JustAGlitchFL/Mix/mix/mix.kicad_sch

## KiCad design mix/mix.kicad_sch (2025-08-01)

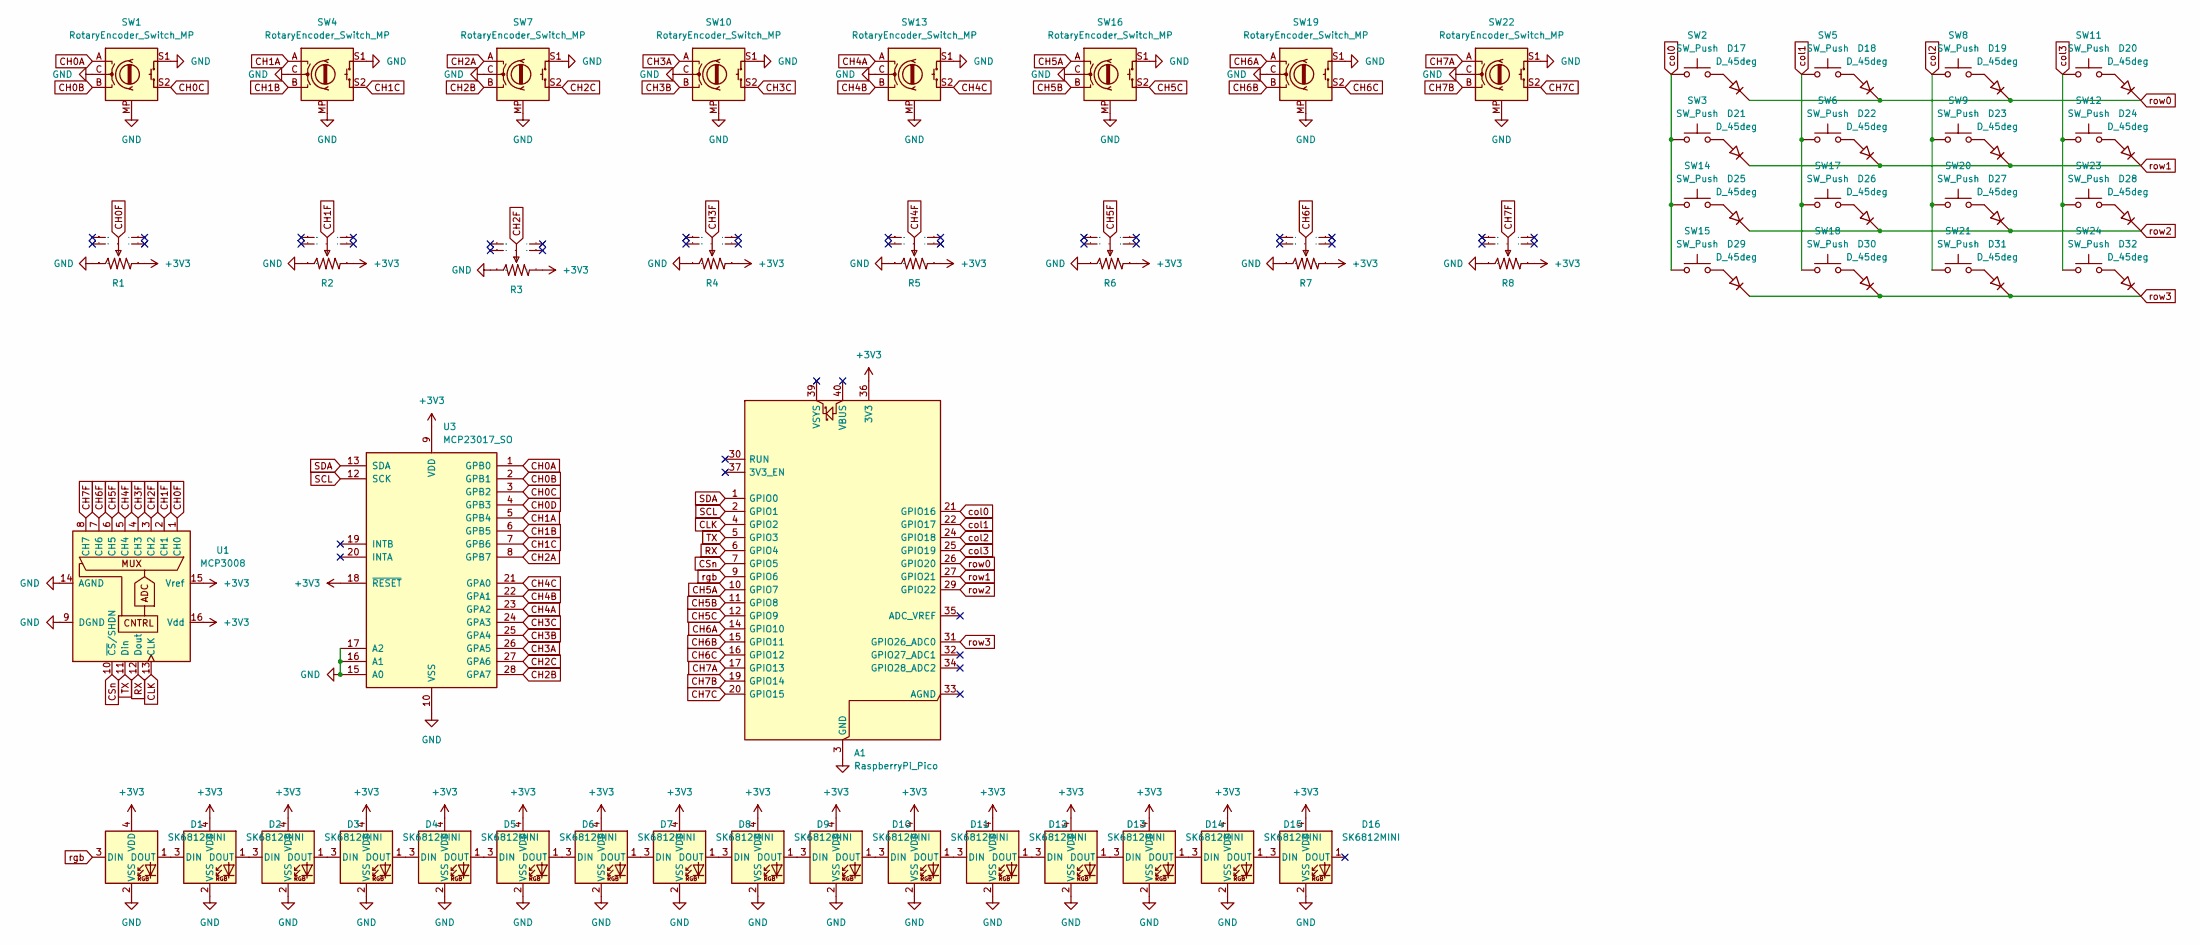
[picture p5: schematic mix.kicad_sch]

Parts:
A1: RaspberryPi_Pico; RaspberryPi_Pico_Common_Unspecified
D1, D2, D3, D4, D5, D6, D7, D8, D9, D10, D11, D12, D13, D14, D15, D16: SK6812MINI; SK6812MINI-E
D17, D18, D19, D20, D21, D22, D23, D24, D25, D26, D27, D28, D29, D30, D31, D32: D_45deg; D_0805_2012Metric_Pad1.15x1.40mm_HandSolder
R1, R2, R3, R4, R5, R6, R7, R8: RES-ADJ_PTA4543-2015CPB102
SW1, SW4, SW7, SW10, SW13, SW16, SW19, SW22: RotaryEncoder_Switch_MP; RotaryEncoder_Alps_EC11E-Switch_Vertical_H20mm_MountingHoles
SW2, SW3, SW5, SW6, SW8, SW9, SW11, SW12, SW14, SW15, SW17, SW18, SW20, SW21, SW23, SW24: SW_Push; SW_Cherry_MX_1.00u_PCB
U1: MCP3008; SOIC-16_3.9x9.9mm_P1.27mm
U3: MCP23017_SO; SOIC-28W_7.5x17.9mm_P1.27mm

Connections:
+3V3: A1.36 (3V3), D1.4 (VDD), D2.4 (VDD), D3.4 (VDD), D4.4 (VDD), D5.4 (VDD), D6.4 (VDD), D7.4 (VDD), D8.4 (VDD), D9.4 (VDD), D10.4 (VDD), D11.4 (VDD), D12.4 (VDD), D13.4 (VDD), D14.4 (VDD), D15.4 (VDD), D16.4 (VDD), R1.3, R2.3, R3.3, R4.3, R5.3, R6.3, R7.3, R8.3, U1.15 (Vref), U1.16 (Vdd), U3.9 (VDD), U3.18 (~RESET)
CH0A: SW1.A, U3.1 (GPB0)
CH0B: SW1.B, U3.2 (GPB1)
CH0C: SW1.S2, U3.3 (GPB2)
CH0D: U3.4 (GPB3)
CH0F: R1.2, U1.1 (CH0)
CH1A: SW4.A, U3.5 (GPB4)
CH1B: SW4.B, U3.6 (GPB5)
CH1C: SW4.S2, U3.7 (GPB6)
CH1F: R2.2, U1.2 (CH1)
CH2A: SW7.A, U3.8 (GPB7)
CH2B: SW7.B, U3.28 (GPA7)
CH2C: SW7.S2, U3.27 (GPA6)
CH2F: R3.2, U1.3 (CH2)
CH3A: SW10.A, U3.26 (GPA5)
CH3B: SW10.B, U3.25 (GPA4)
CH3C: SW10.S2, U3.24 (GPA3)
CH3F: R4.2, U1.4 (CH3)
CH4A: SW13.A, U3.23 (GPA2)
CH4B: SW13.B, U3.22 (GPA1)
CH4C: SW13.S2, U3.21 (GPA0)
CH4F: R5.2, U1.5 (CH4)
CH5A: A1.10 (GPIO7), SW16.A
CH5B: A1.11 (GPIO8), SW16.B
CH5C: A1.12 (GPIO9), SW16.S2
CH5F: R6.2, U1.6 (CH5)
CH6A: A1.14 (GPIO10), SW19.A
CH6B: A1.15 (GPIO11), SW19.B
CH6C: A1.16 (GPIO12), SW19.S2
CH6F: R7.2, U1.7 (CH6)
CH7A: A1.17 (GPIO13), SW22.A
CH7B: A1.19 (GPIO14), SW22.B
CH7C: A1.20 (GPIO15), SW22.S2
CH7F: R8.2, U1.8 (CH7)
CLK: A1.4 (GPIO2), U1.13 (CLK)
CSn: A1.7 (GPIO5), U1.10 (~CS/SHDN)
GND: A1.3 (GND), A1.8 (GND), A1.13 (GND), A1.18 (GND), A1.23 (GND), A1.28 (GND), A1.38 (GND), D1.2 (VSS), D2.2 (VSS), D3.2 (VSS), D4.2 (VSS), D5.2 (VSS), D6.2 (VSS), D7.2 (VSS), D8.2 (VSS), D9.2 (VSS), D10.2 (VSS), D11.2 (VSS), D12.2 (VSS), D13.2 (VSS), D14.2 (VSS), D15.2 (VSS), D16.2 (VSS), R1.1, R2.1, R3.1, R4.1, R5.1, R6.1, R7.1, R8.1, SW1.C, SW1.MP, SW1.S1, SW4.C, SW4.MP, SW4.S1, SW7.C, SW7.MP, SW7.S1, SW10.C, SW10.MP, SW10.S1, SW13.C, SW13.MP, SW13.S1, SW16.C, SW16.MP, SW16.S1, SW19.C, SW19.MP, SW19.S1, SW22.C, SW22.MP, SW22.S1, U1.9 (DGND), U1.14 (AGND), U3.10 (VSS), U3.15 (A0), U3.16 (A1), U3.17 (A2)
unnamed: D1.1 (DOUT), D2.3 (DIN)
unnamed: D2.1 (DOUT), D3.3 (DIN)
unnamed: D3.1 (DOUT), D4.3 (DIN)
unnamed: D4.1 (DOUT), D5.3 (DIN)
unnamed: D5.1 (DOUT), D6.3 (DIN)
unnamed: D6.1 (DOUT), D7.3 (DIN)
unnamed: D7.1 (DOUT), D8.3 (DIN)
unnamed: D8.1 (DOUT), D9.3 (DIN)
unnamed: D10.1 (DOUT), D11.3 (DIN)
unnamed: D9.1 (DOUT), D10.3 (DIN)
unnamed: D11.1 (DOUT), D12.3 (DIN)
unnamed: D12.1 (DOUT), D13.3 (DIN)
unnamed: D13.1 (DOUT), D14.3 (DIN)
unnamed: D14.1 (DOUT), D15.3 (DIN)
unnamed: D15.1 (DOUT), D16.3 (DIN)
unnamed: D17.2 (A), SW2.2
unnamed: D18.2 (A), SW5.2
unnamed: D19.2 (A), SW8.2
unnamed: D20.2 (A), SW11.2
unnamed: D21.2 (A), SW3.2
unnamed: D22.2 (A), SW6.2
unnamed: D23.2 (A), SW9.2
unnamed: D24.2 (A), SW12.2
unnamed: D25.2 (A), SW14.2
unnamed: D26.2 (A), SW17.2
unnamed: D27.2 (A), SW20.2
unnamed: D28.2 (A), SW23.2
unnamed: D29.2 (A), SW15.2
unnamed: D30.2 (A), SW18.2
unnamed: D31.2 (A), SW21.2
unnamed: D32.2 (A), SW24.2
RX: A1.6 (GPIO4), U1.12 (Dout)
SCL: A1.2 (GPIO1), U3.12 (SCK)
SDA: A1.1 (GPIO0), U3.13 (SDA)
TX: A1.5 (GPIO3), U1.11 (Din)
col0: A1.21 (GPIO16), SW2.1, SW3.1, SW14.1, SW15.1
col1: A1.22 (GPIO17), SW5.1, SW6.1, SW17.1, SW18.1
col2: A1.24 (GPIO18), SW8.1, SW9.1, SW20.1, SW21.1
col3: A1.25 (GPIO19), SW11.1, SW12.1, SW23.1, SW24.1
rgb: A1.9 (GPIO6), D1.3 (DIN)
row0: A1.26 (GPIO20), D17.1 (K), D18.1 (K), D19.1 (K), D20.1 (K)
row1: A1.27 (GPIO21), D21.1 (K), D22.1 (K), D23.1 (K), D24.1 (K)
row2: A1.29 (GPIO22), D25.1 (K), D26.1 (K), D27.1 (K), D28.1 (K)
row3: A1.31 (GPIO26_ADC0), D29.1 (K), D30.1 (K), D31.1 (K), D32.1 (K)
